PeppeMinniti/alexo/IMMAGINI/cover.jpeg

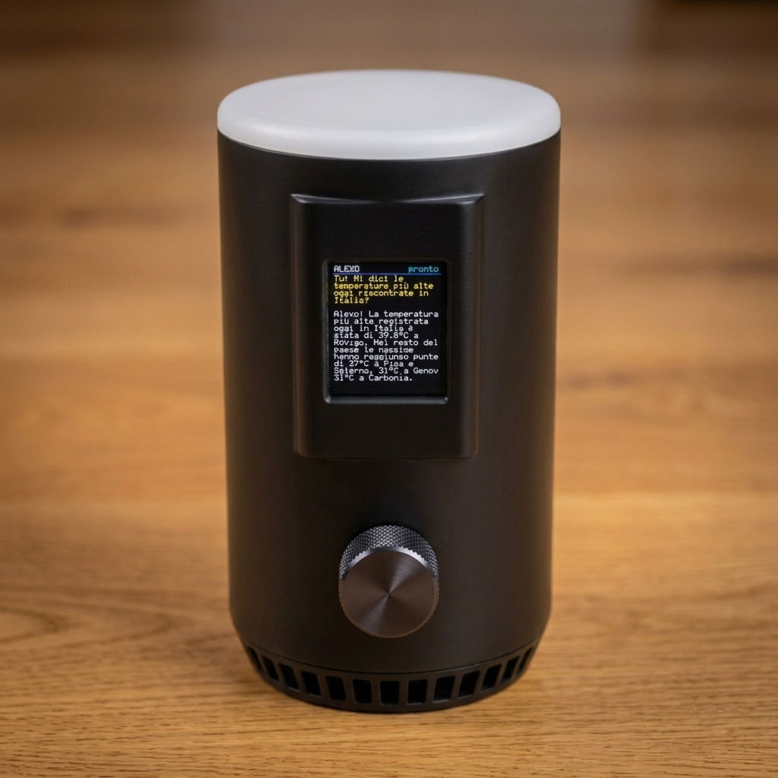
IMMAGINI/cover.jpeg
