PeppeMinniti/alexo/src/wake_model.h

#pragma once
// Modello wake-word microWakeWord v2 "okay_nabu" (esphome/micro-wake-word-models).
// INT8 TFLite. probability_cutoff=0.97 sliding_window_size=5 step=10ms arena~26080.
// Per cambiare wake word (es. "Alexo" custom): sostituisci questo file col nuovo
// .tflite convertito (xxd -i, stesso nome g_wake_model) e aggiorna WAKE_* in config.h.
#include <Arduino.h>

alignas(16) const unsigned char g_wake_model[] = {
  0x1c, 0x00, 0x00, 0x00, 0x54, 0x46, 0x4c, 0x33, 0x14, 0x00, 0x20, 0x00,
  0x1c, 0x00, 0x18, 0x00, 0x14, 0x00, 0x10, 0x00, 0x0c, 0x00, 0x00, 0x00,
  0x08, 0x00, 0x04, 0x00, 0x14, 0x00, 0x00, 0x00, 0x1c, 0x00, 0x00, 0x00,
  0x84, 0x00, 0x00, 0x00, 0xd4, 0x00, 0x00, 0x00, 0x7c, 0x7a, 0x00, 0x00,
  0x8c, 0x7a, 0x00, 0x00, 0x2c, 0xea, 0x00, 0x00, 0x03, 0x00, 0x00, 0x00,
  0x01, 0x00, 0x00, 0x00, 0x04, 0x00, 0x00, 0x00, 0xd6, 0x73, 0xff, 0xff,
  0x0c, 0x00, 0x00, 0x00, 0x1c, 0x00, 0x00, 0x00, 0x38, 0x00, 0x00, 0x00,
  0x0f, 0x00, 0x00, 0x00, 0x73, 0x65, 0x72, 0x76, 0x69, 0x6e, 0x67, 0x5f,
  0x64, 0x65, 0x66, 0x61, 0x75, 0x6c, 0x74, 0x00, 0x01, 0x00, 0x00, 0x00,
  0x04, 0x00, 0x00, 0x00, 0x30, 0x72, 0xff, 0xff, 0x5d, 0x00, 0x00, 0x00,
  0x04, 0x00, 0x00, 0x00, 0x05, 0x00, 0x00, 0x00, 0x64, 0x65, 0x6e, 0x73,
  0x65, 0x00, 0x00, 0x00, 0x01, 0x00, 0x00, 0x00, 0x04, 0x00, 0x00, 0x00,
  0xee, 0x71, 0xff, 0xff, 0x04, 0x00, 0x00, 0x00, 0x0b, 0x00, 0x00, 0x00,
  0x69, 0x6e, 0x70, 0x75, 0x74, 0x5f, 0x61, 0x75, 0x64, 0x69, 0x6f, 0x00,
  0x02, 0x00, 0x00, 0x00, 0x2c, 0x00, 0x00, 0x00, 0x04, 0x00, 0x00, 0x00,
  0x74, 0x72, 0xff, 0xff, 0x6c, 0x00, 0x00, 0x00, 0x04, 0x00, 0x00, 0x00,
  0x13, 0x00, 0x00, 0x00, 0x43, 0x4f, 0x4e, 0x56, 0x45, 0x52, 0x53, 0x49,
  0x4f, 0x4e, 0x5f, 0x4d, 0x45, 0x54, 0x41, 0x44, 0x41, 0x54, 0x41, 0x00,
  0x98, 0x72, 0xff, 0xff, 0x6b, 0x00, 0x00, 0x00, 0x04, 0x00, 0x00, 0x00,
  0x13, 0x00, 0x00, 0x00, 0x6d, 0x69, 0x6e, 0x5f, 0x72, 0x75, 0x6e, 0x74,
  0x69, 0x6d, 0x65, 0x5f, 0x76, 0x65, 0x72, 0x73, 0x69, 0x6f, 0x6e, 0x00,
  0x6d, 0x00, 0x00, 0x00, 0xa4, 0x79, 0x00, 0x00, 0x9c, 0x79, 0x00, 0x00,
  0x7c, 0x79, 0x00, 0x00, 0x5c, 0x79, 0x00, 0x00, 0x3c, 0x79, 0x00, 0x00,
  0x1c, 0x79, 0x00, 0x00, 0xfc, 0x78, 0x00, 0x00, 0xdc, 0x78, 0x00, 0x00,
  0xbc, 0x78, 0x00, 0x00, 0x9c, 0x78, 0x00, 0x00, 0x84, 0x78, 0x00, 0x00,
  0x70, 0x78, 0x00, 0x00, 0x50, 0x78, 0x00, 0x00, 0x30, 0x78, 0x00, 0x00,
  0x10, 0x78, 0x00, 0x00, 0xf0, 0x77, 0x00, 0x00, 0xd0, 0x77, 0x00, 0x00,
  0xb0, 0x77, 0x00, 0x00, 0x90, 0x77, 0x00, 0x00, 0x70, 0x77, 0x00, 0x00,
  0x58, 0x77, 0x00, 0x00, 0x44, 0x77, 0x00, 0x00, 0xb4, 0x75, 0x00, 0x00,
  0xa4, 0x74, 0x00, 0x00, 0x94, 0x64, 0x00, 0x00, 0x84, 0x63, 0x00, 0x00,
  0xb4, 0x5d, 0x00, 0x00, 0xa4, 0x5c, 0x00, 0x00, 0x94, 0x4c, 0x00, 0x00,
  0x04, 0x4c, 0x00, 0x00, 0x14, 0x4a, 0x00, 0x00, 0x84, 0x49, 0x00, 0x00,
  0x54, 0x48, 0x00, 0x00, 0x44, 0x47, 0x00, 0x00, 0x34, 0x37, 0x00, 0x00,
  0xa4, 0x36, 0x00, 0x00, 0x34, 0x35, 0x00, 0x00, 0xa4, 0x34, 0x00, 0x00,
  0xb4, 0x33, 0x00, 0x00, 0xa4, 0x32, 0x00, 0x00, 0x94, 0x2a, 0x00, 0x00,
  0x04, 0x2a, 0x00, 0x00, 0x54, 0x29, 0x00, 0x00, 0x4c, 0x29, 0x00, 0x00,
  0x3c, 0x10, 0x00, 0x00, 0x34, 0x10, 0x00, 0x00, 0x2c, 0x10, 0x00, 0x00,
  0x24, 0x10, 0x00, 0x00, 0x1c, 0x10, 0x00, 0x00, 0x14, 0x10, 0x00, 0x00,
  0x0c, 0x10, 0x00, 0x00, 0x04, 0x10, 0x00, 0x00, 0xfc, 0x0f, 0x00, 0x00,
  0xf4, 0x0f, 0x00, 0x00, 0xec, 0x0f, 0x00, 0x00, 0xe4, 0x0f, 0x00, 0x00,
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
};
const unsigned int g_wake_model_len = 60264;
