PeppeMinniti/alexo/include/secrets.example.h

#pragma once
// ============================================================================
//  ALEXO - Segreti (COPIA questo file in "secrets.h" e compila i valori).
//  secrets.h e' ignorato da git: non finira' mai in un repo pubblico.
// ============================================================================

// --- WiFi -------------------------------------------------------------------
#define WIFI_SSID        "il-tuo-wifi"
#define WIFI_PASSWORD    "la-tua-password"

// --- API key ----------------------------------------------------------------
#define GROQ_API_KEY       "gsk_..."      // Whisper STT (gratis su console.groq.com)
#define OPENAI_API_KEY     "sk-..."       // opzionale (STT/TTS OpenAI)
#define ANTHROPIC_API_KEY  "sk-ant-..."   // Claude (il cervello)
#define ELEVENLABS_API_KEY "sk_..."       // voce TTS (elevenlabs.io)
